LiamOSM/water-watcher/Arduino Code/Flowchart.png

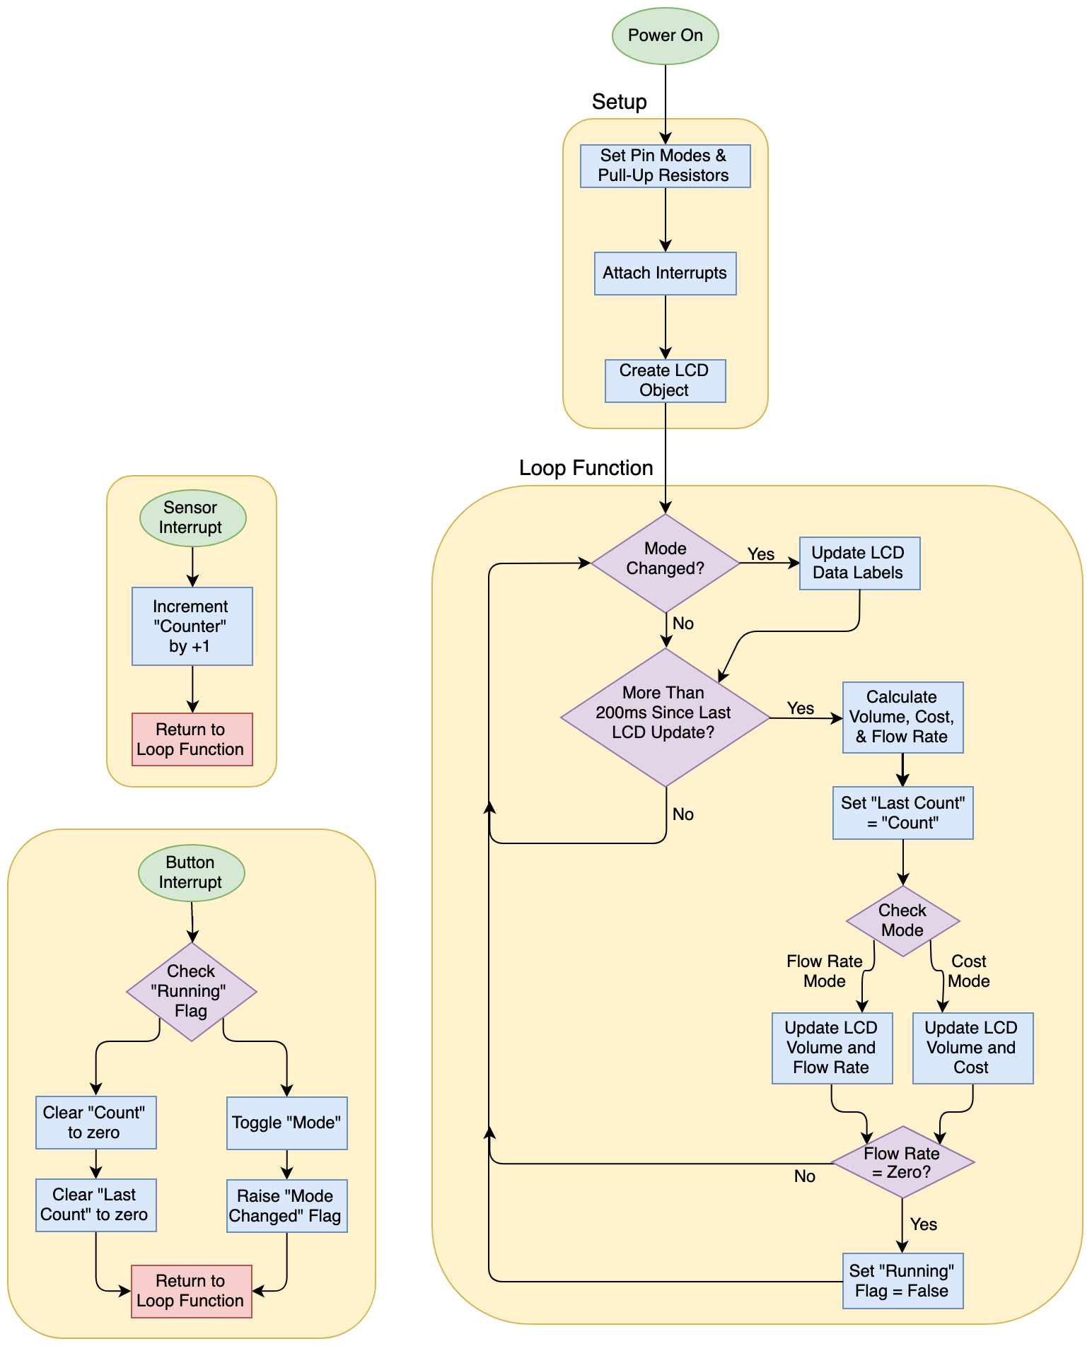
Arduino Code/Flowchart.png
